mvanbrab/water-level/software/WaterLevelReceivers/ReceiverLCDHTTP/secrets_example.h

// Copy this file to secrets.h and change according to instructions below
// ...
// secrets.h: my private credentials and connection details (git-ignored)

#define SECRET_SSID "MySSID"              // replace MySSID with your WiFi network name
#define SECRET_WIFI_PASS "MyPassword"     // replace MyPassword with your WiFi password

#define SECRET_HOSTNAME "myHostname"      // replace myHostname with the host name you define for this device
